flamerten/EG3301RPhysioAid/Misc/M5test/M5test.ino

/*
Board is M5 Atom Stack
IMU code referenced from https://docs.m5stack.com/en/api/atom/mpu
Orientation Filter based on https://courses.cs.washington.edu/courses/cse466/14au/labs/l4/madgwick_internal_report.pdf
Code based on M5 original code

I used the onboard Neopixels as calibration LEDs. I realised that the m5 front was the roll. I think i cant change the axes in anyway 
Hence, i skiped the calibration and relied purely based on the the AHRS wrapper provided
*/


#include <Adafruit_NeoPixel.h> //This is for the onboard LEDs
#include <Wire.h> //I2c for the MPU
#include "M5Atom.h" //helper functions for the MPU

float pitch, roll, yaw; //Stores attitude related variables.

#define READ_DELAY  50 //magdwick filter is effective at low sampling rates
float cal_pitch, cal_roll; //calibration during init;
const uint8_t compare_no = 20; //compare n different readings during calibration
const uint8_t difference = 1; //1 degrees diff between readings = stabalise

//On board LED matrix
#define LED_COUNT 25
#define LED_PIN   27
#define BRIGHTNESS 100 //set as 0 if you do not want to show the indicator
Adafruit_NeoPixel matrix(LED_COUNT,LED_PIN , NEO_GRB + NEO_KHZ800);

void init_matrix(){
  //ensure the matrix behind is turned off, reduce power usage
  //however, this can be useeful as an indicator
  matrix.begin();
  matrix.clear();
  matrix.show();
  matrix.setBrightness(BRIGHTNESS);

}

void light_middle(int r, int g, int b){
  //12 is the centre of the matrix
  matrix.setPixelColor(12,matrix.Color(r,g,b));
  matrix.show();
}


//Calibration Functions that i attempted
void calibrate_IMU(){
  Serial.println("Calibrating");
  light_middle(100,0,0);//light up red during calibration
  cal_pitch = 0;
  cal_roll = 0;

  float max_pitch, max_roll;
  float min_pitch, min_roll;

  max_pitch = max_roll = -200;
  min_pitch = min_roll = 200;

  int num_iter = 50;

  for(int i = 0; i < num_iter; i++){
    M5.IMU.getAhrsData(&pitch,&roll,&yaw);
    
    if(pitch > max_pitch) max_pitch = pitch;
    if(pitch < min_pitch) min_pitch = pitch;
    if(roll > max_roll) max_roll = roll;
    if(roll < min_roll) min_roll = roll;
    
    cal_pitch += pitch;
    cal_roll += roll;
    delay(READ_DELAY);
  }

  cal_pitch = cal_pitch/num_iter;
  cal_roll = cal_roll/num_iter;


  light_middle(0,100,0); //light up green when finished
  Serial.printf("cal_pitch:%.2f, cal_roll:%.2f", cal_pitch,cal_roll);
  Serial.println();
  Serial.printf(
    "PITCH Variation:%.2f , Max_pitch:%.2f, Min_Pitch: %2f",
    max_pitch - min_pitch,
    max_pitch,
    min_pitch
    );
    
  Serial.println();
  Serial.printf(
    "ROLL Variation:%.2f , Max_roll:%.2f, Min_roll: %2f",
    max_roll - min_roll,
    max_roll,
    min_roll
    );

   Serial.println();
   
}

bool arr_is_valid(float diff, float *arr ){
  //check if the diff between max and min is whithin the diff
  
  float max_value = -360.0;
  float min_value = 360.0;
  for(int i = 0; i < compare_no; i++){
    if(arr[i] > max_value) max_value = arr[i];
    if(arr[i] < min_value) min_value = arr[i];
  }

  return abs(max_value - min_value) <= diff;
}

void calibrate_IMU_MAX(){
  //It appears that this is gradient descent. As such i will wait for the readings to be stabalised by comparing the gradients
  light_middle(100,0,0);//light up red during calibration

  Serial.println("Calibrating");
  
  float prev_roll[compare_no];
  float prev_pitch[compare_no];
  int curr_index = 0;
  int count = 0;

  cal_pitch = 0;
  cal_roll = 0;

  while(1){
    M5.IMU.getAhrsData(&pitch,&roll,&yaw);
    
    prev_pitch[curr_index] = pitch;
    prev_roll[curr_index] = roll;

    if(arr_is_valid(difference, prev_roll) && arr_is_valid(difference,prev_pitch)&&count >= compare_no ){
      //check that prev_roll and prev_pitch have stabalised
      //at least compare_no readings are taken to prevent early activation
      for(int i = 0; i  < compare_no; i++){
        cal_pitch += prev_pitch[i];
        cal_roll += prev_roll[i];
      }

      cal_pitch = cal_pitch / compare_no;
      cal_roll = cal_roll / compare_no;

      light_middle(0,100,0); //light up green when finished
      Serial.println("Calibration Done");
      Serial.printf("Cal pitch:%.2f, Cal roll:%.2f", cal_pitch,cal_roll);
      Serial.println();

      return;
    }
    else{
      if(curr_index >= compare_no - 1) curr_index = 0;
      else curr_index++;
      
      count++;
      Serial.println(count);
    }

    delay(READ_DELAY);
  }
  
}

void setup() {
  //Serial Enable baud rate is 115200
  M5.begin(true, true, false); //bool SerialEnable, bool I2CEnable, bool DisplayEnable
  init_matrix();
  M5.IMU.Init();

  //calibrate_IMU_MAX();

}

void loop() {
  
  M5.IMU.getAhrsData(&pitch,&roll,&yaw);
  //pitch -90 to 90degrees
  //roll -180 to 180degrees
  
  /*
  
  Serial.printf("ORGINAL pitch:%.2f, roll:%.2f", pitch,roll);
  Serial.println();
  pitch = pitch - cal_pitch;
  roll = roll - cal_roll;
  Serial.printf("CALIBRATED pitch:%.2f, roll:%.2f", pitch,roll);
  Serial.println();
  */

  //For The serial plotter printout
  //Serial.print(pitch);
  //Serial.print(" ");
  Serial.print(roll);
  Serial.println();
  
  delay(READ_DELAY);

}
